goncalofigueira59/frequency-counter/assets/Fluxograma calcularTensao.png

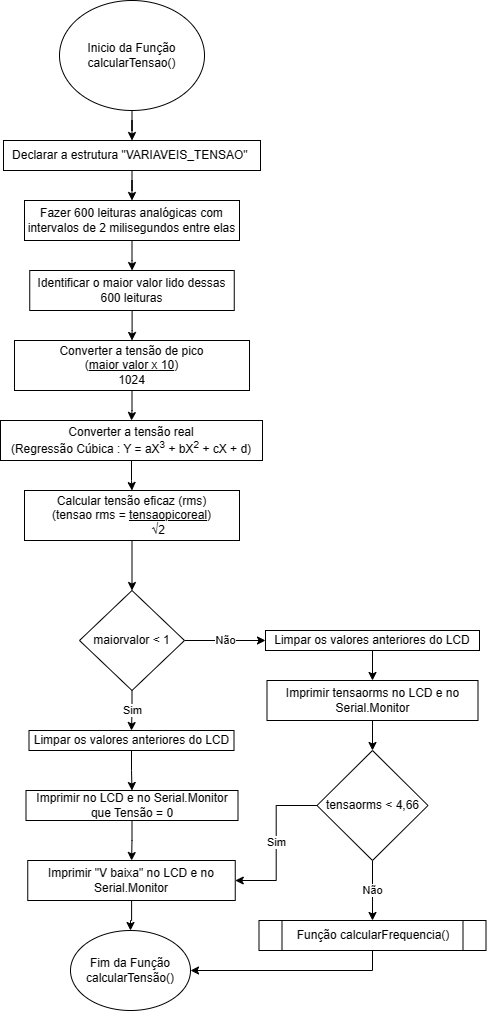
assets/Fluxograma calcularTensao.png
