goncalofigueira59/frequency-counter/assets/Fluxograma Geral.png

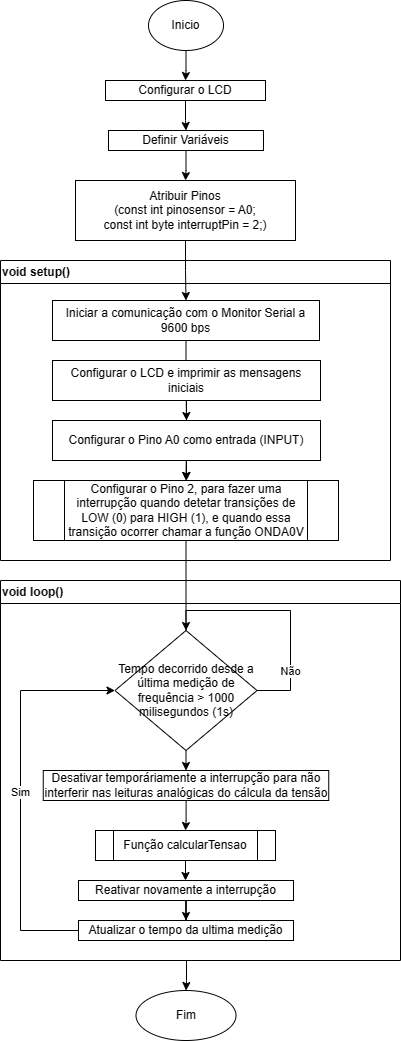
assets/Fluxograma Geral.png
